doates625/RBE-2002-Final-Project/Shaft Collar.SLDPRT

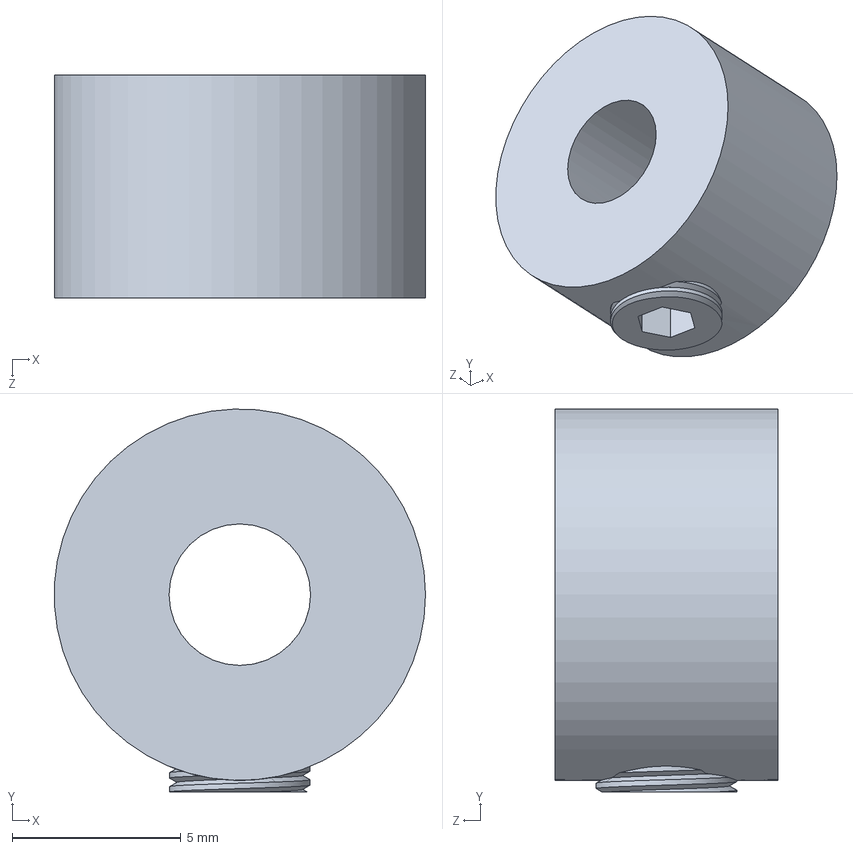
[picture p38: CAD file, 2017-11-07, last stored version]
Shaft Collar.SLDPRT
11.0 x 11.3 x 6.60 mm
