doates625/RBE-2002-Final-Project/top base.SLDPRT

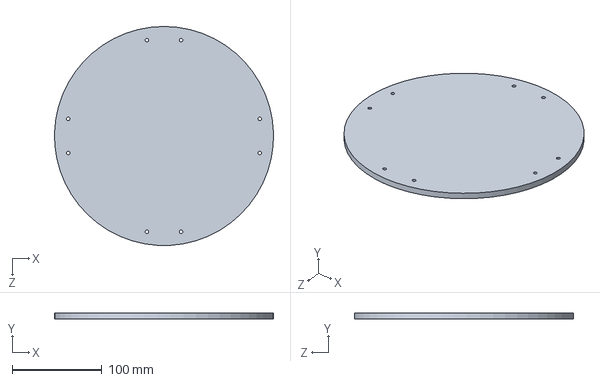
[picture p39: CAD file, 2017-11-07, last stored version]
top base.SLDPRT
244.7 x 6.35 x 244.8 mm
