doates625/RBE-2002-Final-Project/MainBoard/Namespaces/MotorL/MotorL.h

//**************************************************************/
// TITLE
//**************************************************************/

//!t MotorL.h
//!b Namespace for final project robot left drive motor.
//!a Dan Oates (RBE-2002 B17 Team 10)

//!d This namespace contains a DcMotor object for controlling
//!d the left drive wheel and initializes encoder ISRs in its
//!d setup method.

#pragma once
#include "DcMotor.h"

//**************************************************************/
// NAMESPACE DECLARATION
//**************************************************************/

namespace MotorL {
	extern DcMotor motor;
	void setup();
}
