doates625/RBE-2002-Final-Project/MainBoard/Namespaces/MatlabComms/MatlabComms.cpp

//**************************************************************/
// TITLE
//**************************************************************/

//!t MatlabComms.cpp
//!a Dan Oates (RBE-2002 B17 Team 10)

#include "MatlabComms.h"
#include "FireBot.h"
#include "WallFollower.h"
#include "Odometer.h"
#include "Sonar.h"
#include "Hc06.h"
#include "BinarySerial.h"

//**************************************************************/
// NAMESPACE FIELD DEFINITIONS
//**************************************************************/

namespace MatlabComms {

	// Communication Parameters
	HardwareSerial*
		PORT = &Serial;
	const unsigned long
		BAUD = 57600;
	const float
		TIMEOUT = 1.0; // (s)

	// Message Type Byte Definitions
	const byte BYTE_CONNECT = 0x01;
	const byte BYTE_GETDATA = 0x02;
	const byte BYTE_DISCONNECT = 0x03;

	// Communication Interface
	BinarySerial bSerial(*PORT, BAUD);
	Hc06 hc06(*PORT, BAUD);
	Timer timer;
	bool disconnected = false;
}

//**************************************************************/
// NAMESPACE FUNCTION DEFINITIONS
//**************************************************************/

//!b Initializes namespace and tests connection to Hc06.
//!d Call this method in the main setup function.
//!d Returns true of Hc06 is properly connected.
bool MatlabComms::setup() {
	if(hc06.setup()) {
		bSerial.setup();
		return true;
	} else
		return false;
}

//!b Waits for begin message from Matlab.
//!d Returns false if Matlab sent wrong connect byte.
bool MatlabComms::waitForBegin() {
	bSerial.flush();
	bSerial.wait();
	if(bSerial.readByte() == BYTE_CONNECT) {
		bSerial.writeByte(BYTE_CONNECT);
		timer.tic();
		return true;
	} else
		return false;
}

//!b Runs one iteration of Matlab communication loop.
//!d Call this method in the main loop function.
//!d Return codes:
//!d - 0: Complete success
//!d - 1: No message received within timeout
//!d - 2: Invalid message type byte received
uint8_t MatlabComms::loop() {
	if(bSerial.available()) {
		while(bSerial.available()) {

			// Check message type byte
			switch(bSerial.readByte()) {

				// Robot data request
				case BYTE_GETDATA:
					bSerial.writeByte(BYTE_GETDATA);
					bSerial.writeByte(FireBot::getState());
					bSerial.writeByte(WallFollower::getState());
					bSerial.writeFloat(Odometer::position(1));
					bSerial.writeFloat(Odometer::position(2));
					bSerial.writeFloat(Odometer::heading);
					bSerial.writeFloat(Sonar::distF);
					bSerial.writeFloat(Sonar::distB);
					bSerial.writeFloat(Sonar::distL);
					bSerial.writeFloat(Sonar::distR);
					bSerial.writeFloat(FireBot::flamePos(1));
					bSerial.writeFloat(FireBot::flamePos(2));
					bSerial.writeFloat(FireBot::flamePos(3));
					break;

				// Disconnect message
				case BYTE_DISCONNECT:
					disconnected = true;
					break;

				// Invalid message type
				default:
					return 2;
			}
		}
		timer.tic();
	} else {
		if(timer.hasElapsed(TIMEOUT))
			return 1;
	}
	return 0;
}
