doates625/RBE-2002-Final-Project/MainBoard/Namespaces/Odometer/Odometer.h

//**************************************************************/
// TITLE
//**************************************************************/

//!t Odometer.h
//!b Namespace for final project robot odometry system.
//!a Dan Oates (RBE-2002 B17 Team 10)

//!d This namespace uses motor encoders from MotorL and MotorR
//!d and a Bno055 9-DOF IMU to track the robot's heading and
//!d position relative to its starting point.

#pragma once
#include "LinearAtmel.h"

//**************************************************************/
// NAMESPACE DECLARATION
//**************************************************************/

namespace Odometer {
	extern Vec position;
	extern float velocity;
	extern float heading;

	bool setup();
	void loop();
	bool nearHome();
}
