doates625/RBE-2002-Final-Project/MainBoard/Namespaces/PanTilt/PanTilt.h

//**************************************************************/
// TITLE
//**************************************************************/

//!t PanTilt.h
//!b Namespace for final project pan-tilt servo system.
//!a Dan Oates (RBE-2002 B17 Team 10)

//!d This namespace controls the pan-tilt system, consisting of
//!d two DS3218 servo motors controlled via an open-loop servo
//!d control library.

#pragma once
#include "Arduino.h"

//**************************************************************/
// NAMESPACE DECLARATION
//**************************************************************/

namespace PanTilt {
	extern const float PAN_MIN;
	extern const float PAN_MAX;
	extern const float TILT_MIN;
	extern const float TILT_MAX;

	extern float pan;
	extern float tilt;

	void setup();
	void loop();
	void sweep();

	void setPan(float);
	void setTilt(float);
	void stopTilt();

	bool isAimed();
}
