doates625/RBE-2002-Final-Project/MainBoard/.ino.cpp

#ifdef __IN_ECLIPSE__
//This is a automatic generated file
//Please do not modify this file
//If you touch this file your change will be overwritten during the next build
//This file has been generated on 2017-12-15 13:04:21

#include "Arduino.h"
#include "FireBot.h"
void setup() ;
void loop() ;

#include "MainBoard.ino"


#endif
